nickbild/vectron_vga_plus_text_mode/media/text_mode_w_wires.jpg

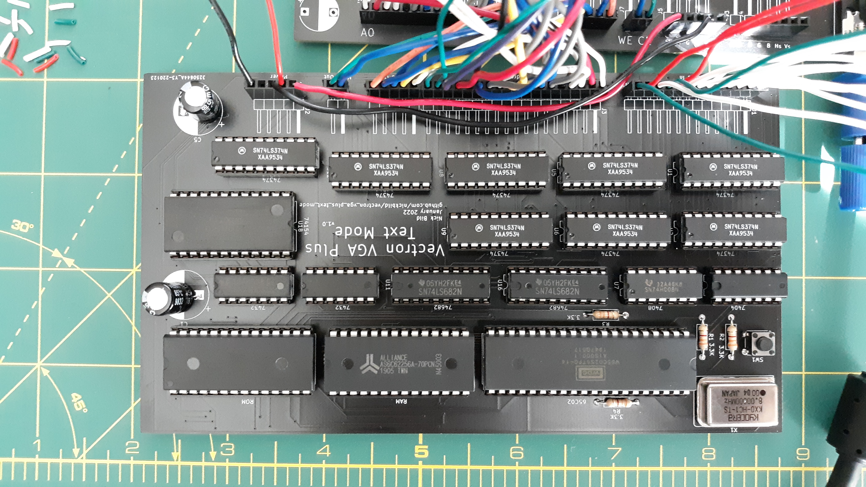
media/text_mode_w_wires.jpg
