nickbild/vectron_vga_plus_text_mode/media/text_mode_with_vga_plus.jpg

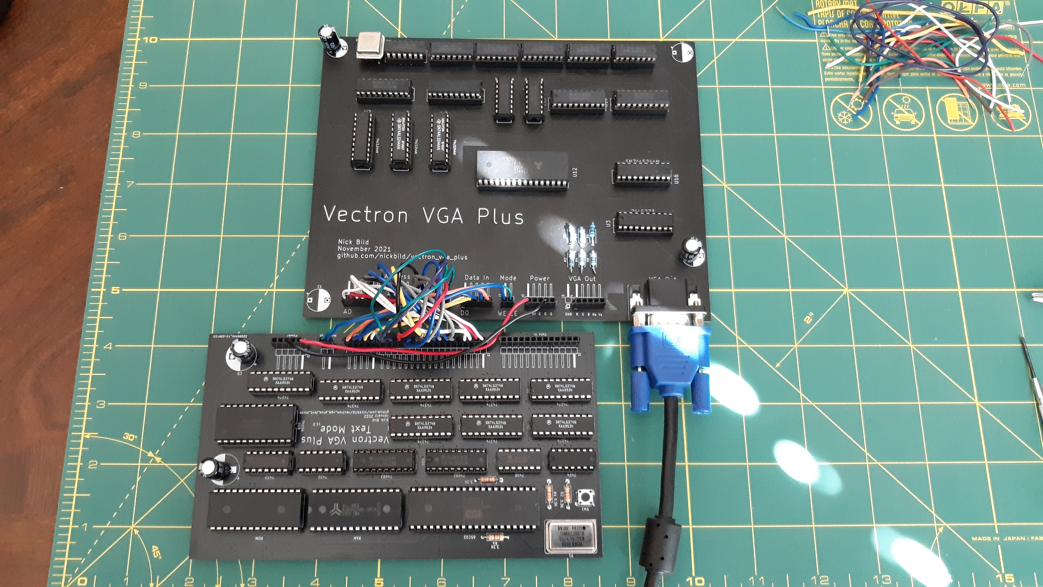
media/text_mode_with_vga_plus.jpg
