nickbild/vectron_vga_plus_text_mode/expand_char_defs.py

from posixpath import split
import re


defs1 = """
CharacterLines1	ORG $9500

	ORG $9501
	.byte #%11111111

	ORG $9520
	.byte #%00000000
	.byte #%00011000
	.byte #%01100110
	.byte #%00100100
	.byte #%00011000
	.byte #%00000000
	.byte #%00000000
	.byte #%00001100
	.byte #%00011000
	.byte #%00001100
	.byte #%00000000
	.byte #%00000000
	.byte #%00000000
	.byte #%00000000
	.byte #%00000000
	.byte #%00000000
	.byte #%00111110
	.byte #%00001100
	.byte #%00111110
	.byte #%00111110
	.byte #%00111000
	.byte #%01111111
	.byte #%00111110
	.byte #%01111111
	.byte #%00111110
	.byte #%00111110
	.byte #%00000000
	.byte #%00000000
	.byte #%00000000
	.byte #%00000000
	.byte #%00000000
	.byte #%00111110
	.byte #%00111110
	.byte #%00011100
	.byte #%00111111
	.byte #%00111110
	.byte #%00011111
	.byte #%01111111
	.byte #%01111111
	.byte #%00111110
	.byte #%01100011
	.byte #%00111110
	.byte #%01111000
	.byte #%00110011
	.byte #%00000011
	.byte #%01100011
	.byte #%01100011
	.byte #%00111110
	.byte #%00111111
	.byte #%00111110
	.byte #%00111111
	.byte #%00111110
	.byte #%00111111
	.byte #%01100011
	.byte #%01100011
	.byte #%01100011
	.byte #%01000001
	.byte #%00110011
	.byte #%00111111

	ORG $955E
	.byte #%00011100
	.byte #%00000000
	.byte #%00000000
	.byte #%00011100
	.byte #%00111111
	.byte #%00111110
	.byte #%00011111
	.byte #%01111111
	.byte #%01111111
	.byte #%00111110
	.byte #%01100011
	.byte #%00111110
	.byte #%01111000
	.byte #%00110011
	.byte #%00000011
	.byte #%01100011
	.byte #%01100011
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
    parseByte(line[55], byteNumber)
    parseByte(line[56], byteNumber)
    parseByte(line[57], byteNumber)
    parseByte(line[58], byteNumber)
    parseByte(line[59], byteNumber)
    parseByte(line[60], byteNumber)
    parseByte(line[61], byteNumber)
    parseByte(line[62], byteNumber)
    parseByte(line[63], byteNumber)
    parseByte(line[64], byteNumber)
    parseByte(line[65], byteNumber)
    print (line[66])
    print (line[67].replace(loc, newLoc))
    parseByte(line[68], byteNumber)
    parseByte(line[69], byteNumber)
    parseByte(line[70], byteNumber)
    parseByte(line[71], byteNumber)
    parseByte(line[72], byteNumber)
    parseByte(line[73], byteNumber)
    parseByte(line[74], byteNumber)
    parseByte(line[75], byteNumber)
    parseByte(line[76], byteNumber)
    parseByte(line[77], byteNumber)
    parseByte(line[78], byteNumber)
    parseByte(line[79], byteNumber)
    parseByte(line[80], byteNumber)
    parseByte(line[81], byteNumber)
    parseByte(line[82], byteNumber)
    parseByte(line[83], byteNumber)
    parseByte(line[84], byteNumber)
    parseByte(line[85], byteNumber)
    parseByte(line[86], byteNumber)
    parseByte(line[87], byteNumber)
    parseByte(line[88], byteNumber)
    parseByte(line[89], byteNumber)
    parseByte(line[90], byteNumber)
    parseByte(line[91], byteNumber)
    parseByte(line[92], byteNumber)
    parseByte(line[93], byteNumber)
    parseByte(line[94], byteNumber)
    parseByte(line[95], byteNumber)
    parseByte(line[96], byteNumber)
    parseByte(line[97], byteNumber)
    parseByte(line[98], byteNumber)
    parseByte(line[99], byteNumber)
    parseByte(line[100], byteNumber)
    parseByte(line[101], byteNumber)
    print (line[102])
    
    return


def parseByte(line, byteNumber):
    line = line.replace("	.byte #%", "")
    pos = 7 - byteNumber
    pixel_value = "#$1F"
    if line[pos] == "0":
        pixel_value = "#$18"
    print("	.byte {0}".format(pixel_value))

    return


processLine(defs1, "95", "95", 0)
processLine(defs2, "96", "96", 0)
processLine(defs3, "97", "97", 0)
processLine(defs4, "98", "98", 0)
processLine(defs5, "99", "99", 0)
processLine(defs6, "9A", "9A", 0)
processLine(defs7, "9B", "9B", 0)
processLine(defs8, "9C", "9C", 0)

processLine(defs1, "95", "9D", 1)
processLine(defs2, "96", "9E", 1)
processLine(defs3, "97", "9F", 1)
processLine(defs4, "98", "A0", 1)
processLine(defs5, "99", "A1", 1)
processLine(defs6, "9A", "A2", 1)
processLine(defs7, "9B", "A3", 1)
processLine(defs8, "9C", "A4", 1)

processLine(defs1, "95", "A5", 2)
processLine(defs2, "96", "A6", 2)
processLine(defs3, "97", "A7", 2)
processLine(defs4, "98", "A8", 2)
processLine(defs5, "99", "A9", 2)
processLine(defs6, "9A", "AA", 2)
processLine(defs7, "9B", "AB", 2)
processLine(defs8, "9C", "AC", 2)

processLine(defs1, "95", "AD", 3)
processLine(defs2, "96", "AE", 3)
processLine(defs3, "97", "AF", 3)
processLine(defs4, "98", "B0", 3)
processLine(defs5, "99", "B1", 3)
processLine(defs6, "9A", "B2", 3)
processLine(defs7, "9B", "B3", 3)
processLine(defs8, "9C", "B4", 3)

processLine(defs1, "95", "B5", 4)
processLine(defs2, "96", "B6", 4)
processLine(defs3, "97", "B7", 4)
processLine(defs4, "98", "B8", 4)
processLine(defs5, "99", "B9", 4)
processLine(defs6, "9A", "BA", 4)
processLine(defs7, "9B", "BB", 4)
processLine(defs8, "9C", "BC", 4)


processLine(defs1, "95", "BD", 5)
processLine(defs2, "96", "BE", 5)
processLine(defs3, "97", "BF", 5)
processLine(defs4, "98", "C0", 5)
processLine(defs5, "99", "C1", 5)
processLine(defs6, "9A", "C2", 5)
processLine(defs7, "9B", "C3", 5)
processLine(defs8, "9C", "C4", 5)


processLine(defs1, "95", "C5", 6)
processLine(defs2, "96", "C6", 6)
processLine(defs3, "97", "C7", 6)
processLine(defs4, "98", "C8", 6)
processLine(defs5, "99", "C9", 6)
processLine(defs6, "9A", "CA", 6)
processLine(defs7, "9B", "CB", 6)
processLine(defs8, "9C", "CC", 6)

processLine(defs1, "95", "CD", 7)
processLine(defs2, "96", "CE", 7)
processLine(defs3, "97", "CF", 7)
processLine(defs4, "98", "D0", 7)
processLine(defs5, "99", "D1", 7)
processLine(defs6, "9A", "D2", 7)
processLine(defs7, "9B", "D3", 7)
processLine(defs8, "9C", "D4", 7)
